mcilhargey/PocketCHIP-PCB/v1_0/PCB/PocketCHIP-v1.0.sch

## EAGLE design v1_0/PCB/PocketCHIP-v1.0.sch (2016-06-02)

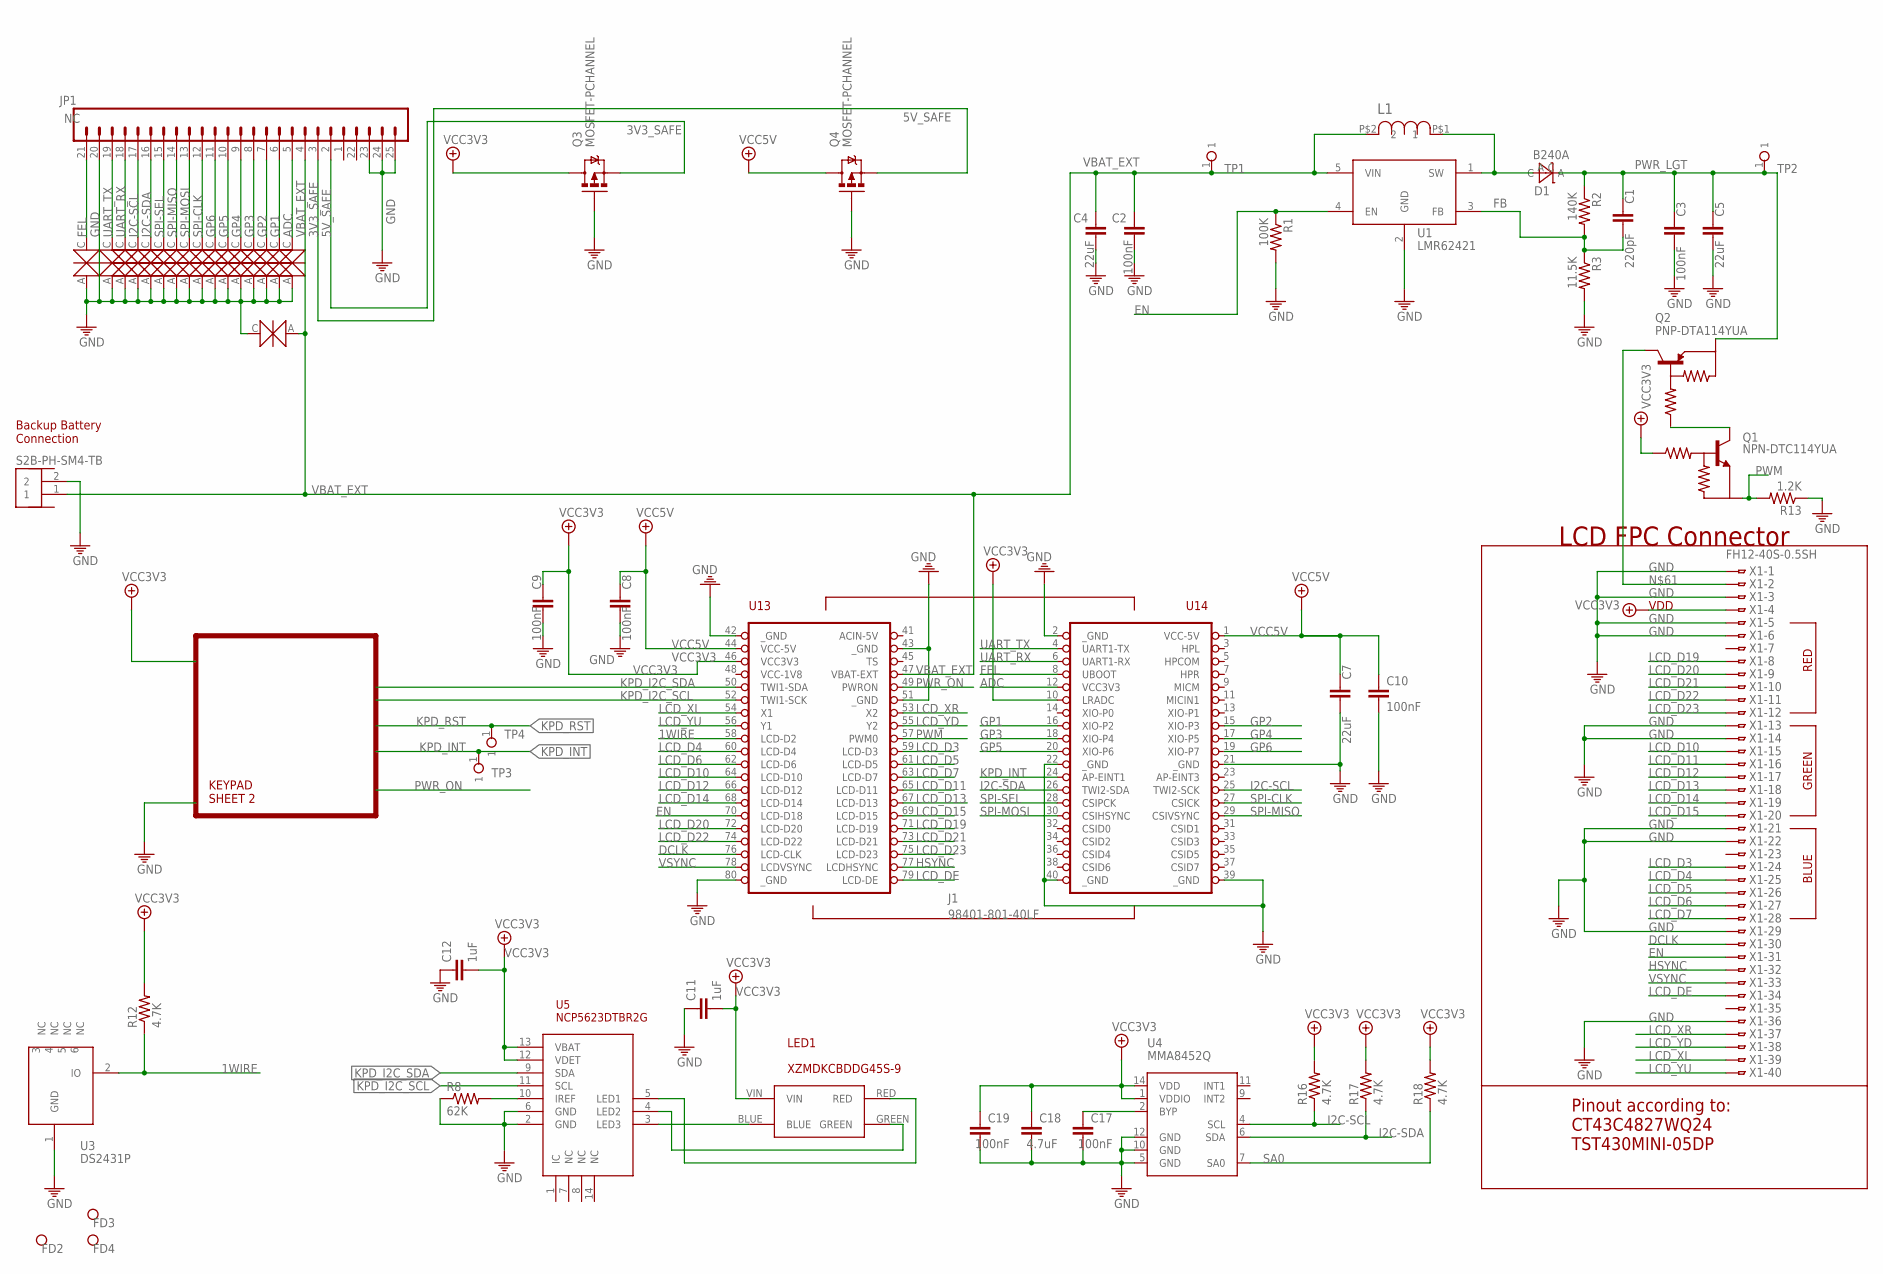
[picture p10: schematic PocketCHIP-v1.0.sch, sheet 1]

Parts:
C1: 220pF; C0402
C2, C3, C8, C9, C10, C17, C19: 100nF; C0402
C4, C5, C7: 22uF; C1206
C11, C12: 1uF; C0402
C18: 4.7uF; C0402
D1: B240A; DO-214AC
ESD1, ESD2, ESD3, ESD4, ESD5, ESD6, ESD7, ESD8, ESD9, ESD10, ESD11, ESD12, ESD13, ESD14, ESD15, ESD16, ESD17: ESD5Z2.5T1G; SOD523
FD2, FD3, FD4: FIDUCIAL; FIDUCIAL_1MM
J1: 98401-801-40LF
J3: S2B-PH-SM4-TB
JP1: NC; 1X20_LOCK_LONGPADS
L1: SRN6045-100M; SRN6045
LED1: XZMDKCBDDG45S-9
Q1: NPN-DTC114YUA; SOT323
Q2: PNP-DTA114YUA; SOT323
Q3, Q4: MOSFET-PCHANNEL; SOT23-3
R1: 100K; R0402
R2: 140K; R0402
R3: 11.5K; R0402
R8: 62K; R0402
R12, R16, R17, R18: 4.7K; R0402
R13: 1.2K; R0402
TP1, TP2, TP3, TP4: N.C; TP_19_5
U1: LMR62421; SOT23-5
U3: DS2431P; TSOC6
U4: MMA8452Q; QFN-16_0.5MM
U5: NCP5623DTBR2G; TSSOP14
X1: FH12-40S-0.5SH

Connections:
1WIRE: J1.58 (LCD-D2), R12.1, U3.2 (IO)
3V3_SAFE: JP1.2, Q3.2 (S)
5V_SAFE: JP1.3, Q4.2 (S)
ADC: ESD16.C, J1.12 (VCC3V3), JP1.5
DCLK: J1.76 (LCD-CLK), X1.30
EN: J1.70 (LCD-D18), R1.1, U1.4 (EN), X1.31
FB: C1.2, R2.2, R3.1, U1.3 (FB)
FEL: ESD1.C, J1.8 (UBOOT), JP1.21
GND: C2.2, C3.2, C4.2, C5.2, C7.2, C8.2, C9.2, C10.2, C11.1, C12.1, C17.2, C18.2, C19.2, ESD1.A, ESD2.A, ESD3.A, ESD4.A, ESD5.A, ESD6.A, ESD7.A, ESD8.A, ESD9.A, ESD10.A, ESD11.A, ESD12.A, ESD13.A, ESD14.A, ESD15.A, ESD16.A, ESD17.C, J1.2 (_GND), J1.21 (_GND), J1.22 (_GND), J1.39 (_GND), J1.40 (_GND), J1.42 (_GND), J1.43 (_GND), J1.51 (_GND), J1.80 (_GND), J3.2, JP1.20, JP1.23, JP1.24, JP1.25, Q3.1 (G), Q4.1 (G), R1.2, R3.2, R8.1, R13.1, U1.2 (GND), U3.1 (GND), U4.5 (GND), U4.10 (GND), U4.12 (GND), U5.2 (GND), U5.6 (GND), X1.1, X1.3, X1.5, X1.6, X1.13, X1.14, X1.21, X1.22, X1.29, X1.36
GP1: ESD15.C, J1.16 (XIO-P2), JP1.6
GP2: ESD14.C, J1.15 (XIO-P3), JP1.7
GP3: ESD13.C, J1.18 (XIO-P4), JP1.8
GP4: ESD12.C, J1.17 (XIO-P5), JP1.9
GP5: ESD11.C, J1.20 (XIO-P6), JP1.10
GP6: ESD10.C, J1.19 (XIO-P7), JP1.11
HSYNC: J1.77 (LCDHSYNC), X1.32
I2C-SCL: ESD4.C, J1.25 (TWI2-SCK), JP1.17, R16.1, U4.4 (SCL)
I2C-SDA: ESD5.C, J1.26 (TWI2-SDA), JP1.16, R17.1, U4.6 (SDA)
KPD_I2C_SCL: J1.52 (TWI1-SCK), U5.11 (SCL)
KPD_I2C_SDA: J1.50 (TWI1-SDA), U5.9 (SDA)
KPD_INT: J1.24 (AP-EINT1), TP3.1
KPD_RST: TP4.1
LCD_D3: J1.59 (LCD-D3), X1.24
LCD_D4: J1.60 (LCD-D4), X1.25
LCD_D5: J1.61 (LCD-D5), X1.26
LCD_D6: J1.62 (LCD-D6), X1.27
LCD_D7: J1.63 (LCD-D7), X1.28
LCD_D10: J1.64 (LCD-D10), X1.15
LCD_D11: J1.65 (LCD-D11), X1.16
LCD_D12: J1.66 (LCD-D12), X1.17
LCD_D13: J1.67 (LCD-D13), X1.18
LCD_D14: J1.68 (LCD-D14), X1.19
LCD_D15: J1.69 (LCD-D15), X1.20
LCD_D19: J1.71 (LCD-D19), X1.8
LCD_D20: J1.72 (LCD-D20), X1.9
LCD_D21: J1.73 (LCD-D21), X1.10
LCD_D22: J1.74 (LCD-D22), X1.11
LCD_D23: J1.75 (LCD-D23), X1.12
LCD_DE: J1.79 (LCD-DE), X1.34
LCD_XL: J1.54 (X1), X1.39
LCD_XR: J1.53 (X2), X1.37
LCD_YD: J1.55 (Y2), X1.38
LCD_YU: J1.56 (Y1), X1.40
unnamed: C17.1, U4.2 (BYP)
unnamed: LED1.GREEN, U5.4 (LED2)
unnamed: LED1.RED, U5.5 (LED1)
unnamed: R8.2, U5.10 (IREF)
unnamed: Q2.3 (OUT), X1.2
unnamed: Q1.3 (OUT), Q2.1 (IN)
unnamed: LED1.BLUE, U5.3 (LED3)
PWM: J1.57 (PWM0), Q1.2 (GND), R13.2
PWR_LGT: C1.1, C3.1, C5.1, D1.C, Q2.2 (GND), R2.1, TP2.1
PWR_ON: J1.49 (PWRON)
SA0: R18.1, U4.7 (SA0)
SPI-CLK: ESD9.C, J1.27 (CSICK), JP1.12
SPI-MISO: ESD7.C, J1.29 (CSIVSYNC), JP1.14
SPI-MOSI: ESD8.C, J1.30 (CSIHSYNC), JP1.13
SPI-SEL: ESD6.C, J1.28 (CSIPCK), JP1.15
UART_RX: ESD3.C, J1.6 (UART1-RX), JP1.18
UART_TX: ESD2.C, J1.4 (UART1-TX), JP1.19
VBAT_EXT: C2.1, C4.1, ESD17.A, J1.47 (VBAT-EXT), J3.1, JP1.4, L1.P$2 (2), TP1.1, U1.5 (VIN)
VCC3V3: C9.1, C11.2, C12.2, C18.1, C19.1, J1.10 (LRADC), J1.46 (VCC3V3), LED1.VIN, Q1.1 (IN), Q3.3 (D), R12.2, R16.2, R17.2, R18.2, U4.1 (VDDIO), U4.14 (VDD), U5.12 (VDET), U5.13 (VBAT), X1.4
VCC5V: C7.1, C8.1, C10.1, J1.1 (VCC-5V), J1.44 (VCC-5V), Q4.3 (D)
VREG_OUTPUT: D1.A, L1.P$1 (1), U1.1 (SW)
VSYNC: J1.78 (LCDVSYNC), X1.33

Notes on the sheet:
LCD FPC Connector
KEYPAD SHEET 2
VDD
RED
GREEN
BLUE
Pinout according to: CT43C4827WQ24 TST430MINI-05DP
Backup Battery Connection

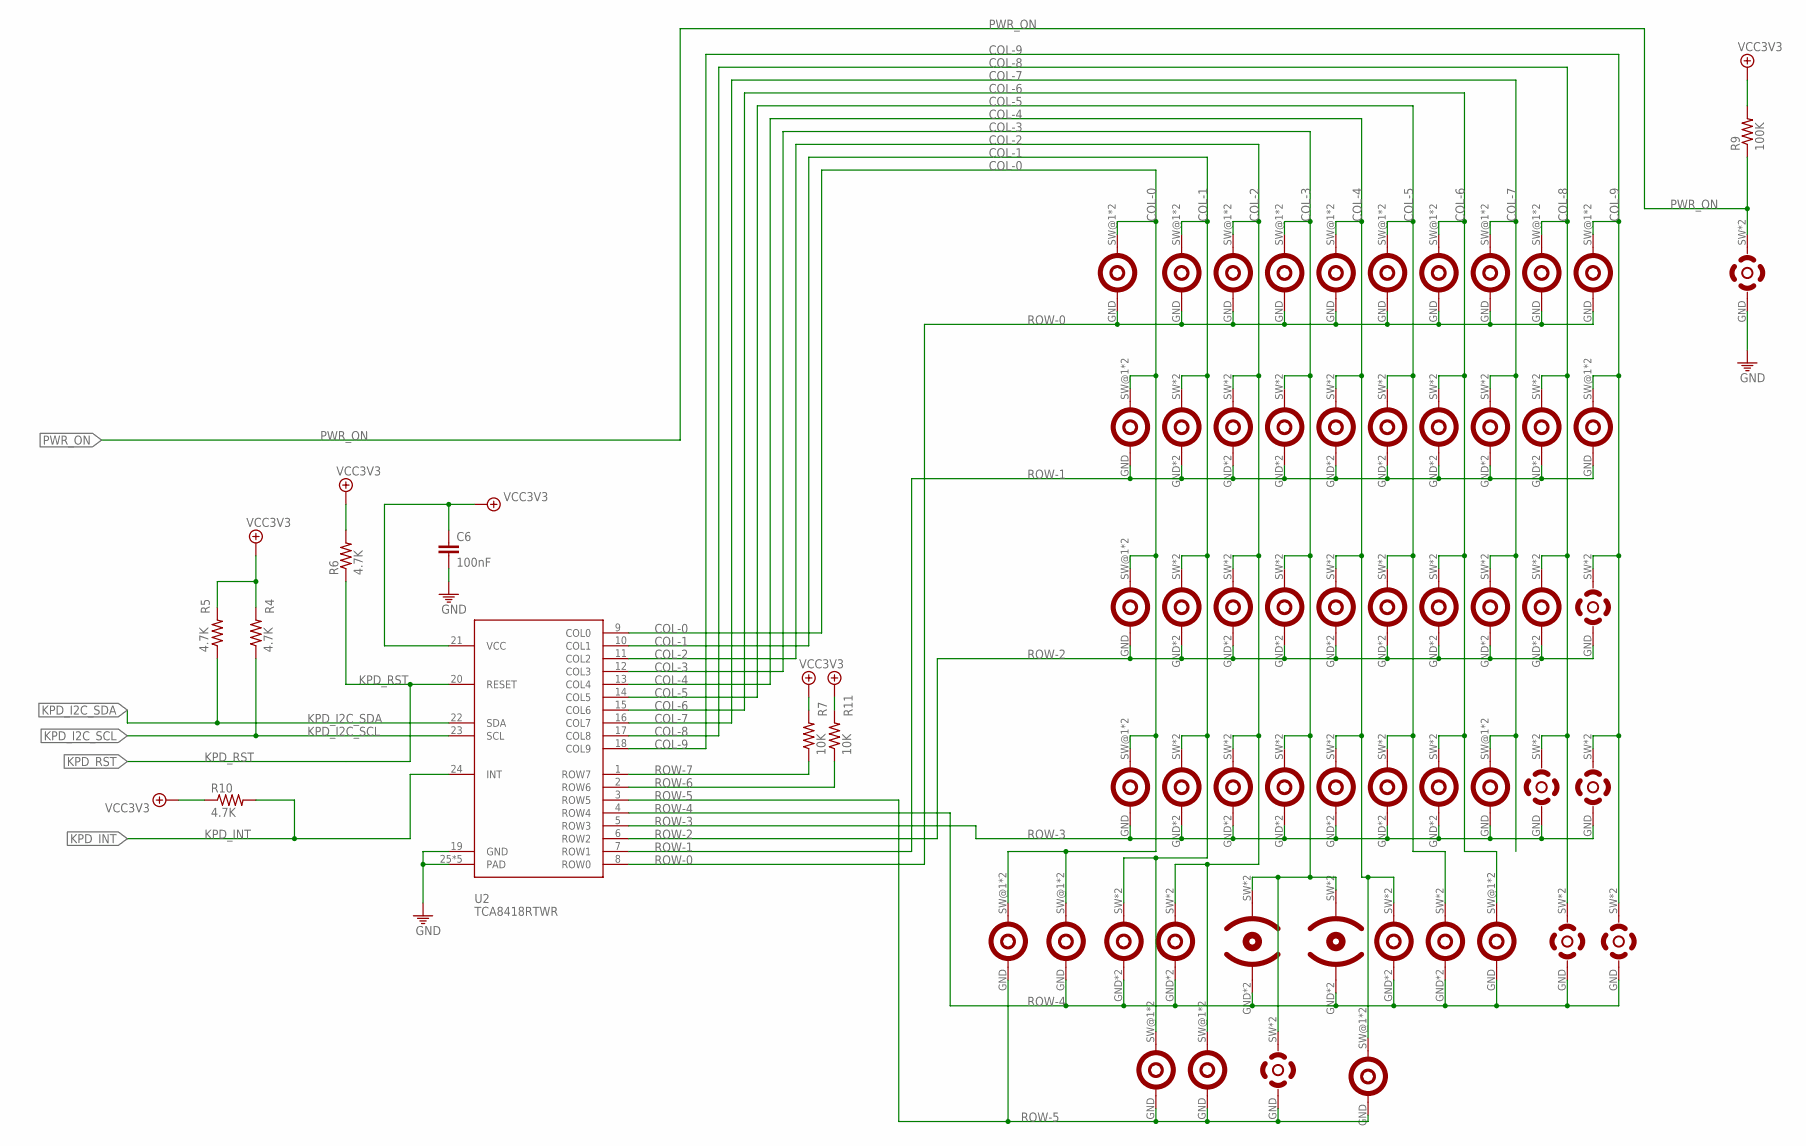
[picture p11: schematic PocketCHIP-v1.0.sch, sheet 2]

Parts:
0, 1, 2, 3, 4, 5, 6, 7, 8, 9: M272201PAD; SNAPDOME_M27220_1PAD
': M272201PAD; SNAPDOME_M27220_1PAD
+: M272201PAD; SNAPDOME_M27220_1PAD
-: M272201PAD; SNAPDOME_M27220_1PAD
?/: M27220; SNAPDOME_M27220
A: M272201PAD; SNAPDOME_M27220_1PAD
ALT: M27220; SNAPDOME_M27220
B: M27220; SNAPDOME_M27220
BKSPC: BL08260; SNAPDOME_BL08260
C: M27220; SNAPDOME_M27220
C6: 100nF; C0402
CTRL: M272201PAD; SNAPDOME_M27220_1PAD
D: M27220; SNAPDOME_M27220
DWN: E9-TDF-340; SNAPDOME_E9-TDF-340
E: M27220; SNAPDOME_M27220
ENTER: BL08260; SNAPDOME_BL08260
ESC: M272201PAD; SNAPDOME_M27220_1PAD
F: M27220; SNAPDOME_M27220
FN: M27220; SNAPDOME_M27220
G: M27220; SNAPDOME_M27220
H: M27220; SNAPDOME_M27220
I: M27220; SNAPDOME_M27220
J: M27220; SNAPDOME_M27220
K: M27220; SNAPDOME_M27220
L: M27220; SNAPDOME_M27220
LEFT: E9-TDF-340; SNAPDOME_E9-TDF-340
M: M272201PAD; SNAPDOME_M27220_1PAD
N: M27220; SNAPDOME_M27220
O: M27220; SNAPDOME_M27220
P: M272201PAD; SNAPDOME_M27220_1PAD
PWR: 100105; SNAPDOME_100105
Q: M272201PAD; SNAPDOME_M27220_1PAD
R: M27220; SNAPDOME_M27220
R4, R5, R6, R10: 4.7K; R0402
R7, R11: 10K; R0402
R9: 100K; R0402
RIGHT: E9-TDF-340; SNAPDOME_E9-TDF-340
S: M27220; SNAPDOME_M27220
SHFT: M272201PAD; SNAPDOME_M27220_1PAD
SHIFT: M272201PAD; SNAPDOME_M27220_1PAD
SPACEL: E.22-ONN-230; SNAPDOME_E.22-ONN-230
SPACER: E.22-ONN-230; SNAPDOME_E.22-ONN-230
T: M27220; SNAPDOME_M27220
TAB: M27220; SNAPDOME_M27220
U: M27220; SNAPDOME_M27220
U2: TCA8418RTWR; WQFN24
UP: E9-TDF-340; SNAPDOME_E9-TDF-340
V: M27220; SNAPDOME_M27220
W: M27220; SNAPDOME_M27220
X: M27220; SNAPDOME_M27220
Y: M27220; SNAPDOME_M27220
Z: M27220; SNAPDOME_M27220

Connections:
COL-0: 1.SW@1 (SW), A.SW@1 (SW), CTRL.SW@1 (SW), ESC.SW@1 (SW), Q.SW@1 (SW), SHIFT.SW@1 (SW), U2.9 (COL0)
COL-1: 2.SW@1 (SW), -.SW@1 (SW), FN.SW, S.SW, U2.10 (COL1), W.SW, Z.SW
COL-2: 3.SW@1 (SW), +.SW@1 (SW), ALT.SW, D.SW, E.SW, U2.11 (COL2), X.SW
COL-3: 4.SW@1 (SW), BKSPC.SW, C.SW, F.SW, R.SW, SPACEL.SW, SPACER.SW, U2.12 (COL3)
COL-4: 5.SW@1 (SW), '.SW@1 (SW), G.SW, T.SW, TAB.SW, U2.13 (COL4), V.SW
COL-5: 6.SW@1 (SW), ?/.SW, B.SW, H.SW, U2.14 (COL5), Y.SW
COL-6: 7.SW@1 (SW), J.SW, N.SW, SHFT.SW@1 (SW), U.SW, U2.15 (COL6)
COL-7: 8.SW@1 (SW), I.SW, K.SW, M.SW@1 (SW), U2.16 (COL7)
COL-8: 9.SW@1 (SW), L.SW, LEFT.SW, O.SW, U2.17 (COL8), UP.SW
COL-9: 0.SW@1 (SW), DWN.SW, ENTER.SW, P.SW@1 (SW), RIGHT.SW, U2.18 (COL9)
GND: C6.2, PWR.GND, U2.19 (GND), U2.25 (PAD)
KPD_I2C_SCL: R4.1, U2.23 (SCL)
KPD_I2C_SDA: R5.1, U2.22 (SDA)
KPD_INT: R10.2, U2.24 (INT)
KPD_RST: R6.1, U2.20 (RESET)
PWR_ON: PWR.SW, R9.1
ROW-0: 0.GND, 1.GND, 2.GND, 3.GND, 4.GND, 5.GND, 6.GND, 7.GND, 8.GND, 9.GND, U2.8 (ROW0)
ROW-1: E.GND, I.GND, O.GND, P.GND, Q.GND, R.GND, T.GND, U.GND, U2.7 (ROW1), W.GND, Y.GND
ROW-2: A.GND, D.GND, ENTER.GND, F.GND, G.GND, H.GND, J.GND, K.GND, L.GND, S.GND, U2.6 (ROW2)
ROW-3: B.GND, C.GND, DWN.GND, M.GND, N.GND, SHIFT.GND, U2.5 (ROW3), UP.GND, V.GND, X.GND, Z.GND
ROW-4: ?/.GND, ALT.GND, ESC.GND, FN.GND, LEFT.GND, RIGHT.GND, SHFT.GND, SPACEL.GND, SPACER.GND, TAB.GND, U2.4 (ROW4)
ROW-5: '.GND, +.GND, -.GND, BKSPC.GND, CTRL.GND, U2.3 (ROW5)
ROW-6: R11.1, U2.2 (ROW6)
ROW-7: R7.1, U2.1 (ROW7)
VCC3V3: C6.1, R4.2, R5.2, R6.2, R7.2, R9.2, R10.1, R11.2, U2.21 (VCC)
